FT-Autonomous/ft_ads/Mounting System CAD/Useful Resources/Zed2i Reference Images/Explorer_HD720_SN38337619_14-21-39.png

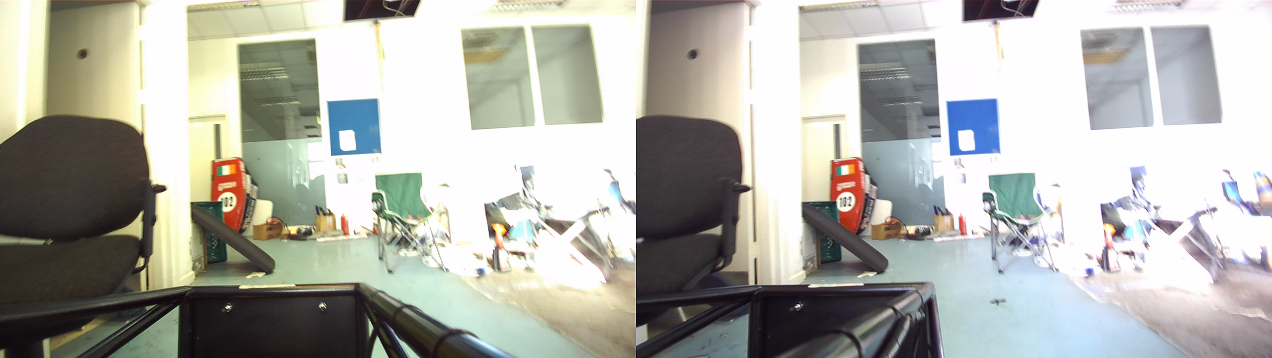
Mounting System CAD/Useful Resources/Zed2i Reference Images/Explorer_HD720_SN38337619_14-21-39.png
