FT-Autonomous/ft_ads/Mounting System CAD/Chassis Addition Parts/FrontLongBar_40x40x3Thin+InclinedSection.SLDPRT

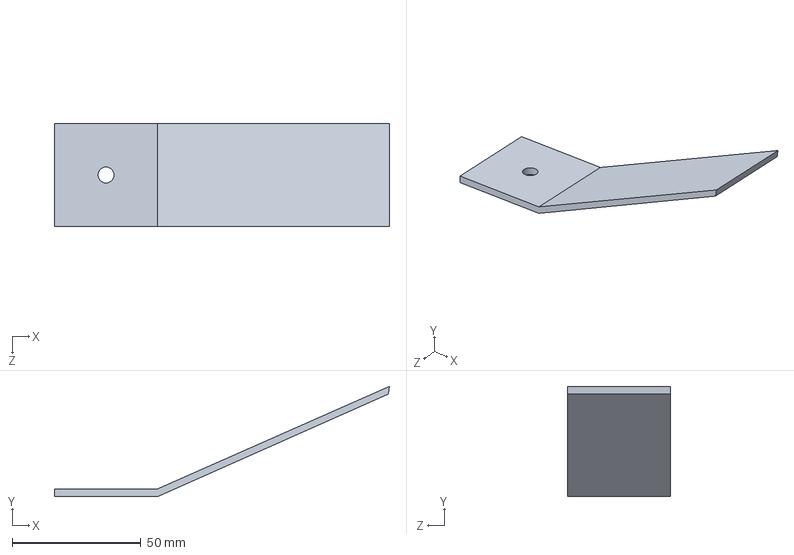
[picture p30: CAD file, 2026-04-02]
Mounting System CAD/Chassis Addition Parts/FrontLongBar_40x40x3Thin+InclinedSection.SLDPRT
130.1 x 42.8 x 40.0 mm
