FT-Autonomous/ft_ads/Mounting System CAD/What Needs To Fit/Lidar Box.SLDPRT

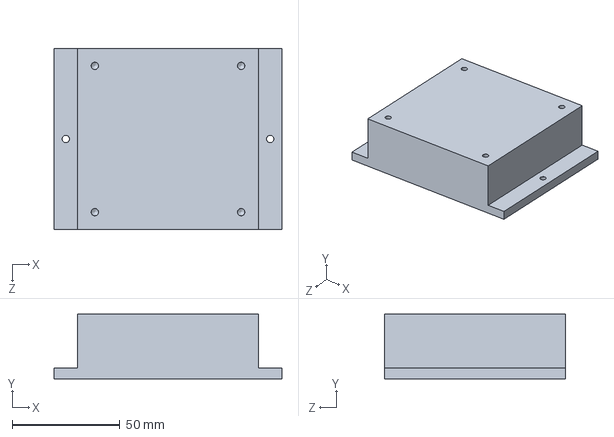
[picture p31: CAD file, 2026-02-10]
Mounting System CAD/What Needs To Fit/Lidar Box.SLDPRT
106.0 x 30.0 x 84.0 mm
