FT-Autonomous/ft_ads/Mounting System CAD/ZED2i mount/Mount_L_bracket.SLDPRT

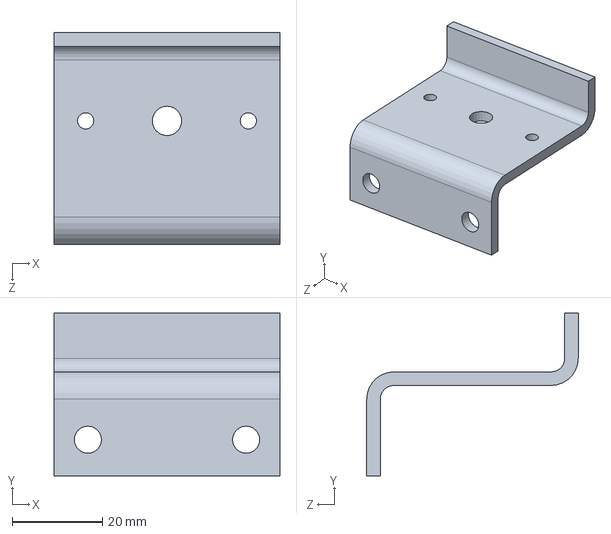
[picture p32: CAD file, 2026-04-07]
Mounting System CAD/ZED2i mount/Mount_L_bracket.SLDPRT
50.0 x 36.0 x 46.8 mm
