FT-Autonomous/ft_ads/Mounting System CAD/mount.SLDPRT

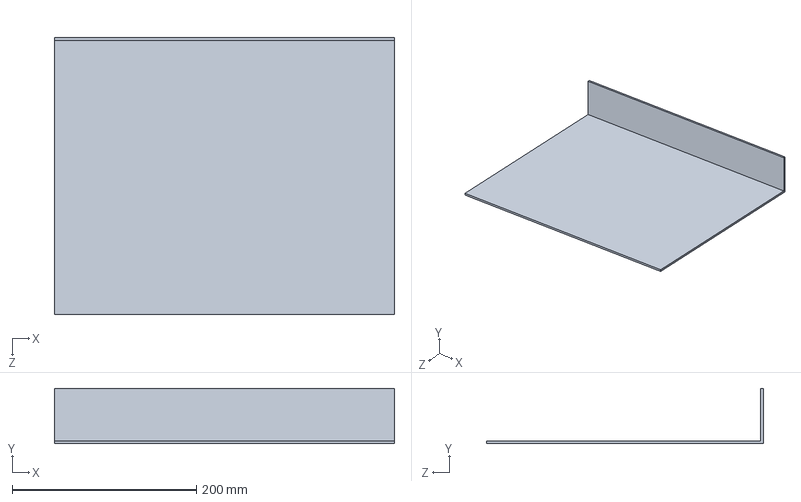
[picture p33: CAD file, 2026-03-31]
Mounting System CAD/mount.SLDPRT
368.7 x 59.9 x 300.0 mm
