FT-Autonomous/ft_ads/Mounting System CAD/basebasebaseplate.SLDPRT

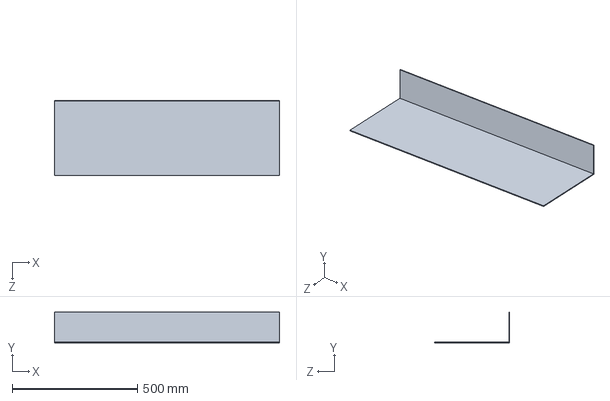
[picture p34: CAD file, 2026-03-31]
Mounting System CAD/basebasebaseplate.SLDPRT
900.0 x 123.3 x 300.0 mm
