FT-Autonomous/ft_ads/Mounting System CAD/Baseplate updated.SLDPRT

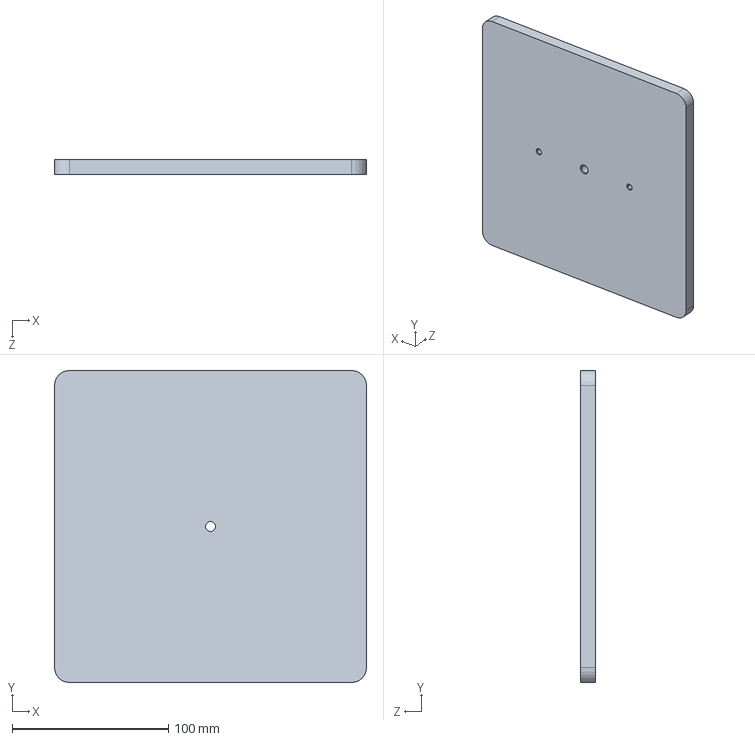
[picture p35: CAD file, 2026-03-24]
Mounting System CAD/Baseplate updated.SLDPRT
200.0 x 200.0 x 9.50 mm
