FT-Autonomous/ft_ads/Mounting System CAD/camera mount.SLDPRT

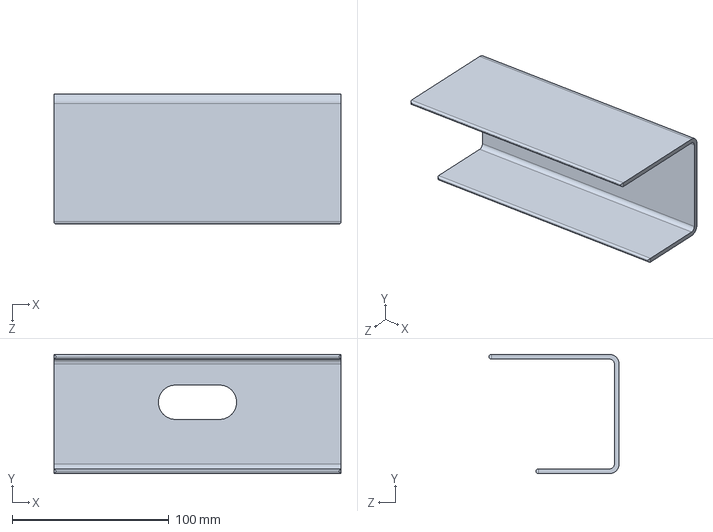
[picture p36: CAD file, 2026-02-24]
Mounting System CAD/camera mount.SLDPRT
183.0 x 76.0 x 83.0 mm
