FT-Autonomous/ft_ads/Mounting System CAD/lidar and cone.SLDASM

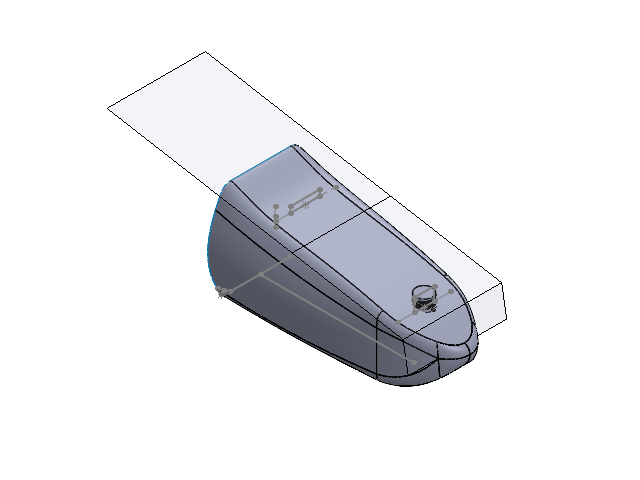
[picture p40: CAD file, 2026-02-19]
Mounting System CAD/lidar and cone.SLDASM
FTX6_Nosecone_with_Rough_Sensor_Placements
LiDAR
