FT-Autonomous/ft_ads/kiCad/ads_circuit_schematic/ads_circuit_schematic.kicad_sch

## KiCad design kiCad/ads_circuit_schematic/ads_circuit_schematic.kicad_sch (2026-02-26)

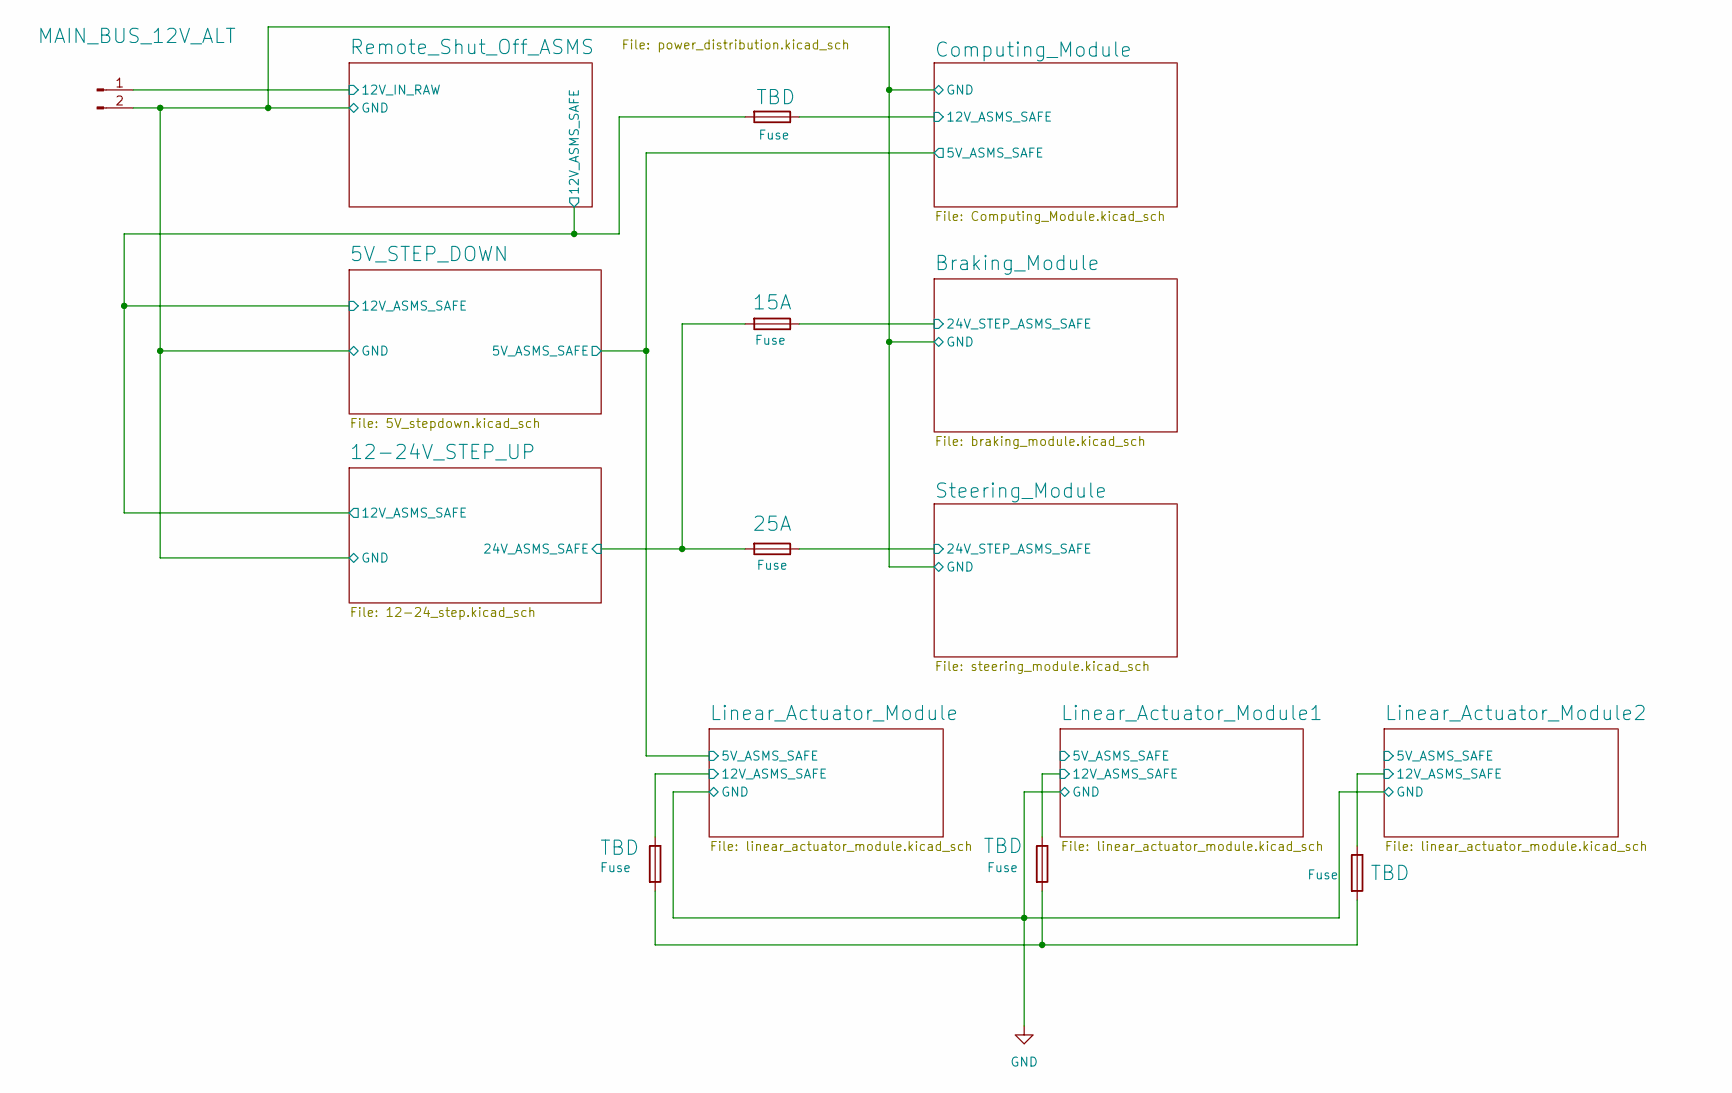
[picture p41: schematic ads_circuit_schematic.kicad_sch]

Parts:
15A, 25A: Fuse
MAIN_BUS_12V_ALT: Conn_01x02_Pin
TBD: Fuse

Connections:
12V_ASMS_SAFE: TBD.1, TBD.2
12V_IN_RAW: MAIN_BUS_12V_ALT.1
24V_ASMS_SAFE: 15A.2, 25A.2
24V_STEP_ASMS_SAFE: 15A.1, 25A.1
GND: MAIN_BUS_12V_ALT.2
