FT-Autonomous/ft_ads/kiCad/ads_circuit_schematic/linear_actuator_module.kicad_sch

## KiCad design kiCad/ads_circuit_schematic/linear_actuator_module.kicad_sch (2026-03-24)

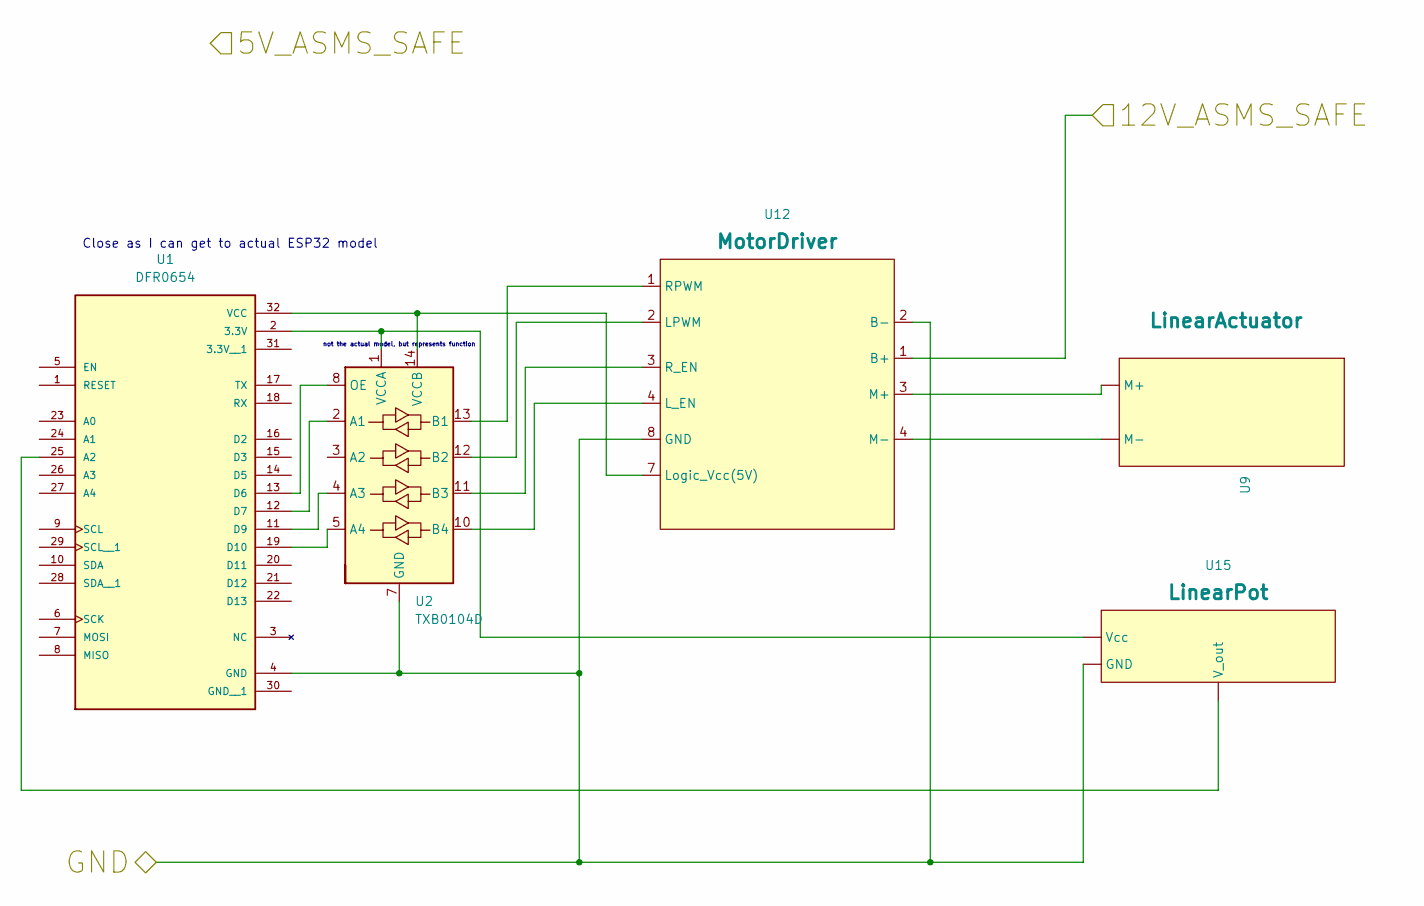
[picture p42: schematic linear_actuator_module.kicad_sch]

Parts:
U1: DFR0654; MODULE_DFR0654
U2: TXB0104D; SOIC-14_3.9x8.7mm_P1.27mm
U9: LinearActuator
U12: MotorDriver
U15: LinearPot

Connections:
12V_ASMS_SAFE: U12.1 (RPWM)
GND: U1.4 (GND), U2.7 (GND), U12.2 (LPWM), U12.8 (GND), U15.
unnamed: U1.2 (3.3V), U2.1 (VCCA), U15.
unnamed: U1.11 (D9), U2.4 (A3)
unnamed: U1.12 (D7), U2.2 (A1)
unnamed: U1.13 (D6), U2.8 (OE)
unnamed: U1.19 (D10), U2.5 (A4)
unnamed: U1.25 (A2), U15.
unnamed: U1.32 (VCC), U2.14 (VCCB), U12.7 (Logic_Vcc(5V))
unnamed: U2.13 (B1), U12.1 (RPWM)
unnamed: U2.12 (B2), U12.2 (LPWM)
unnamed: U2.11 (B3), U9., U12.3 (R_EN)
unnamed: U2.10 (B4), U9., U12.4 (L_EN)

Notes on the sheet:
Close as I can get to actual ESP32 model
not the actual model, but represents function
