FT-Autonomous/ft_ads/kiCad/ads_circuit_schematic/steering_module.kicad_sch

## KiCad design kiCad/ads_circuit_schematic/steering_module.kicad_sch (2026-03-02)

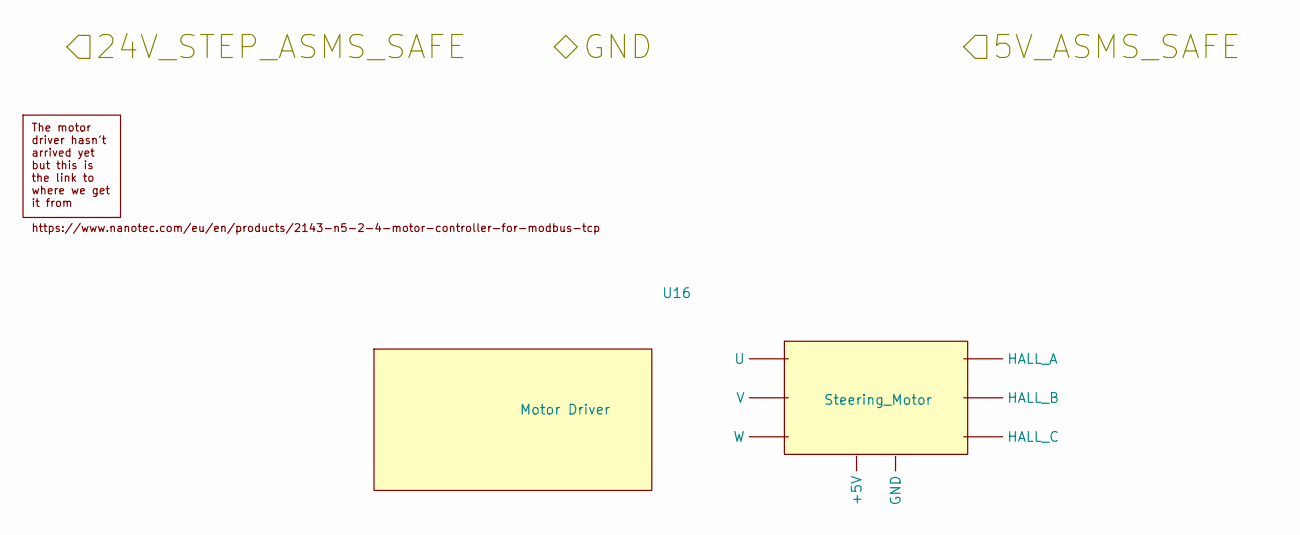
[picture p43: schematic steering_module.kicad_sch]

Parts:
Steering_Motor: (no value)
U16: Motor Driver
