FT-Autonomous/ft_ads/kiCad/fsuk-ads-electrical/SDC.kicad_sch

## KiCad design kiCad/fsuk-ads-electrical/SDC.kicad_sch (2026-07-04)

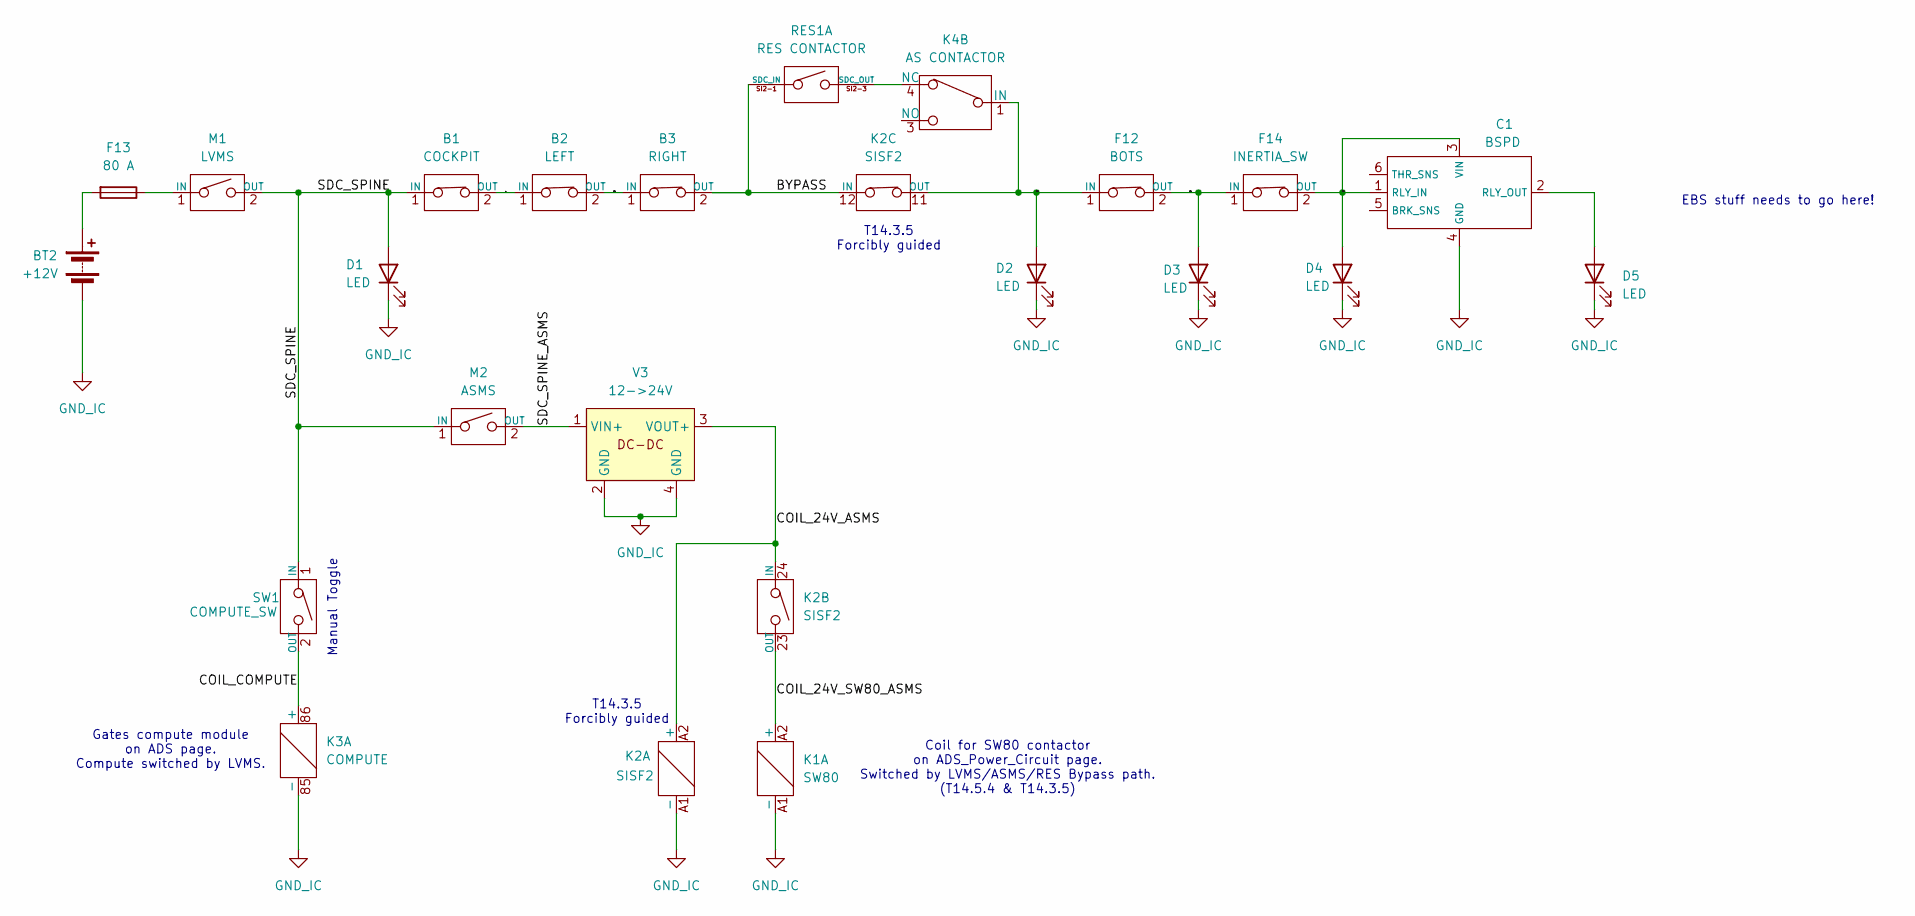
[picture p44: schematic SDC.kicad_sch]

Parts:
B1: COCKPIT
B2: LEFT
B3: RIGHT
BT2: +12V
C1: BSPD
D1, D2, D3, D4, D5: LED
F12: BOTS
F13: 80 A
F14: INERTIA_SW
K1: SW80
K2: SISF2
K3: COMPUTE
K4: AS CONTACTOR
M1: LVMS
M2: ASMS
RES1: RES CONTACTOR
SW1: COMPUTE_SW
V3: 12->24V

Connections:
BYPASS: B3.2 (OUT), K2.12 (IN), RES1.SI2-1 (SDC_IN)
COIL_24V_ASMS: K2.24 (IN), K2.A2 (+), V3.3 (VOUT+)
COIL_24V_SW80_ASMS: K1.A2 (+), K2.23 (OUT)
COIL_COMPUTE: K3.86 (+), SW1.2 (OUT)
GND_IC: BT2.2 (-), C1.4 (GND), D1.1 (K), D2.1 (K), D3.1 (K), D4.1 (K), D5.1 (K), K1.A1 (-), K2.A1 (-), K3.85 (-), V3.2 (GND), V3.4 (GND)
unnamed: BT2.1 (+), F13.2
unnamed: C1.2 (RLY_OUT), D5.2 (A)
unnamed: F13.1, M1.1 (IN)
unnamed: K4.4 (NC), RES1.SI2-3 (SDC_OUT)
SDC_1: B1.2 (OUT), B2.1 (IN)
SDC_2: B2.2 (OUT), B3.1 (IN)
SDC_3: D2.2 (A), F12.1 (IN), K2.11 (OUT), K4.1 (IN)
SDC_4: D3.2 (A), F12.2 (OUT), F14.1 (IN)
SDC_5: C1.1 (RLY_IN), C1.3 (VIN), D4.2 (A), F14.2 (OUT)
SDC_SPINE: B1.1 (IN), D1.2 (A), M1.2 (OUT), M2.1 (IN), SW1.1 (IN)
SDC_SPINE_ASMS: M2.2 (OUT), V3.1 (VIN+)

Notes on the sheet:
Manual Toggle
EBS stuff needs to go here!
T14.3.5 Forcibly guided
Coil for SW80 contactor on ADS_Power_Circuit page. Switched by LVMS/ASMS/RES Bypass path. (T14.5.4 & T14.3.5)
Gates compute module on ADS page. Compute switched by LVMS.
