FT-Autonomous/ft_ads/kiCad/fsuk-ads-electrical/ads_power_circuit.kicad_sch

## KiCad design kiCad/fsuk-ads-electrical/ads_power_circuit.kicad_sch (2026-07-04, an earlier design)

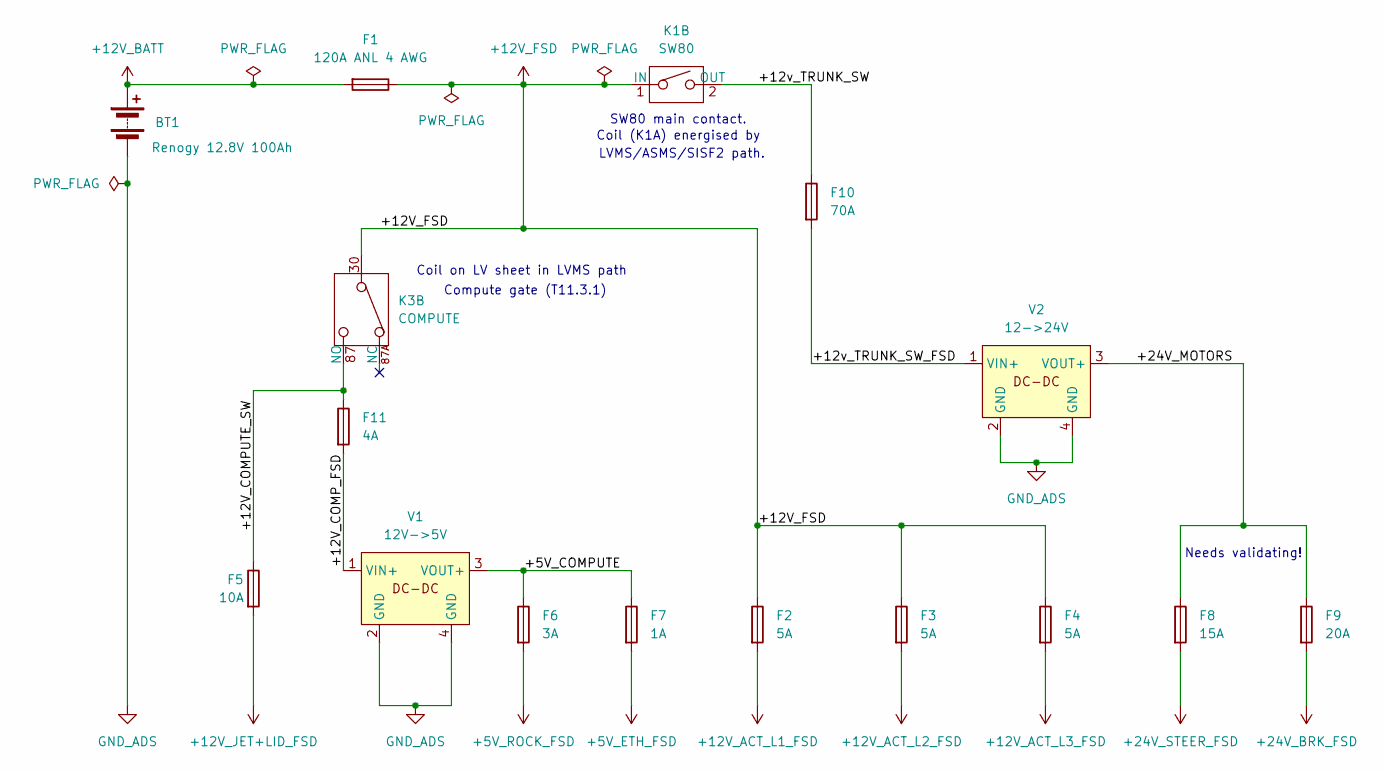
[picture p45: schematic ads_power_circuit.kicad_sch]

Parts:
BT1: Renogy 12.8V 100Ah
F1: 120A ANL 4 AWG
F2, F3, F4: 5A
F5: 10A
F6: 3A
F7: 1A
F8: 15A
F9: 20A
F10: 70A
F11: 4A
K1: SW80
K3: COMPUTE
V1: 12V->5V
V2: 12->24V

Connections:
+5V_COMPUTE: F6.1, F7.1, V1.3 (VOUT+)
+5V_ETH_FSD: F7.2
+5V_ROCK_FSD: F6.2
+12V_ACT_L1_FSD: F2.2
+12V_ACT_L2_FSD: F3.2
+12V_ACT_L3_FSD: F4.2
+12V_BATT: BT1.1 (+), F1.2
+12V_COMPUTE_SW: F5.1, F11.1, K3.87 (NO)
+12V_COMP_FSD: F11.2, V1.1 (VIN+)
+12V_FSD: F1.1, F2.1, F3.1, F4.1, K1.1 (IN), K3.30
+12V_JET+LID_FSD: F5.2
+12v_TRUNK_SW: F10.1, K1.2 (OUT)
+12v_TRUNK_SW_FSD: F10.2, V2.1 (VIN+)
+24V_BRK_FSD: F9.2
+24V_MOTORS: F8.1, F9.1, V2.3 (VOUT+)
+24V_STEER_FSD: F8.2
GND_ADS: BT1.2 (-), V1.2 (GND), V1.4 (GND), V2.2 (GND), V2.4 (GND)

Notes on the sheet:
Needs validating!
Compute gate (T11.3.1)
LVMS/ASMS/SISF2 path.
Coil on LV sheet in LVMS path
Coil (K1A) energised by
SW80 main contact.
